Bridge12Technologies/OpenPCBLGR/Model/91780A023.SLDPRT

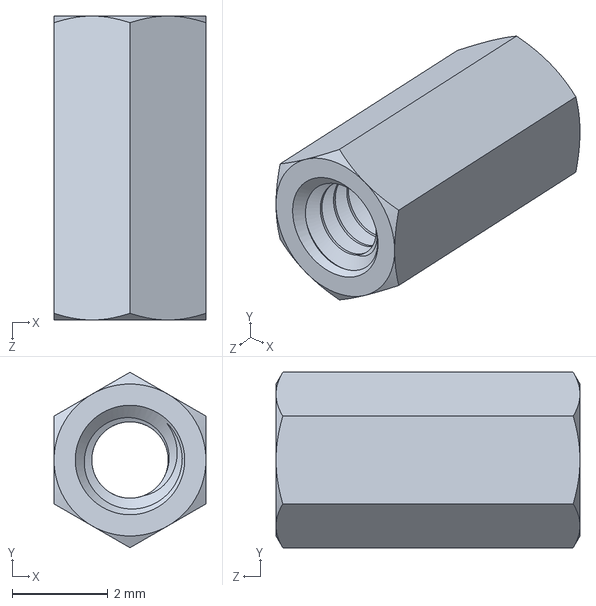
[picture p16: CAD file, 2022-07-21]
Model/91780A023.SLDPRT
3.17 x 3.67 x 6.35 mm
