Bridge12Technologies/OpenPCBLGR/Model/121003110.SLDPRT

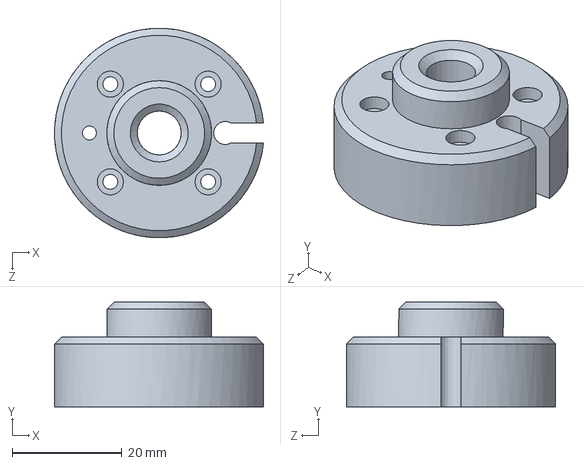
[picture p17: CAD file, 2022-07-21]
Model/121003110.SLDPRT
38.0 x 19.1 x 38.1 mm
