Bridge12Technologies/OpenPCBLGR/KiCAD/5mm_X-Band_LGR/X-Band_EPR_LGR.sch

## KiCad design KiCAD/5mm_X-Band_LGR/X-Band_EPR_LGR.sch (2022-07-21)

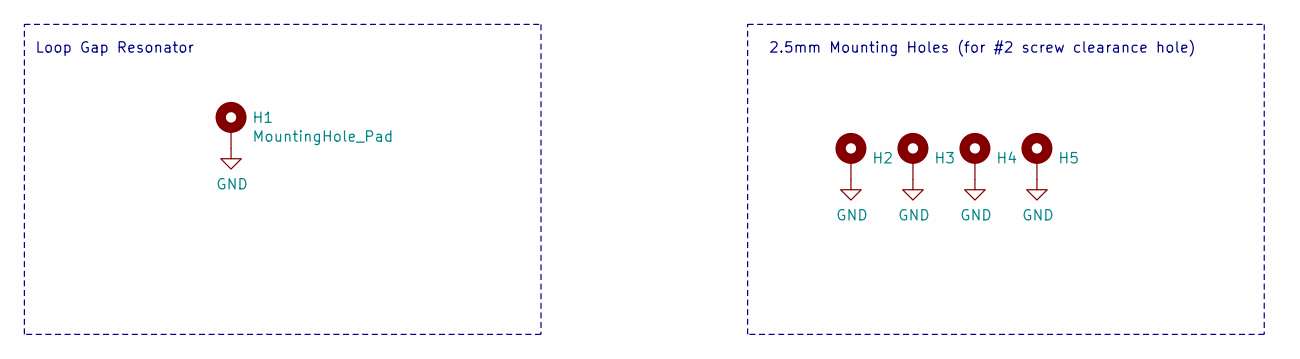
[picture p18: schematic X-Band_EPR_LGR.sch]

Parts:
H1: MountingHole_Pad; 5.2mm_3L2G_X-Band
H2, H3, H4, H5: MountingHole_Pad; MountingHole_2.5mm_Pad

Connections:
GND: H1.1, H2.1, H3.1, H4.1, H5.1

Notes on the sheet:
Loop Gap Resonator
2.5mm Mounting Holes (for #2 screw clearance hole)
