Bridge12Technologies/OpenPCBLGR/KiCAD/5mm_X-Band_LGR_BOTTOM/X-Band_EPR_LGR_BOTTOM.sch

## KiCad design KiCAD/5mm_X-Band_LGR_BOTTOM/X-Band_EPR_LGR_BOTTOM.sch (2022-07-21)

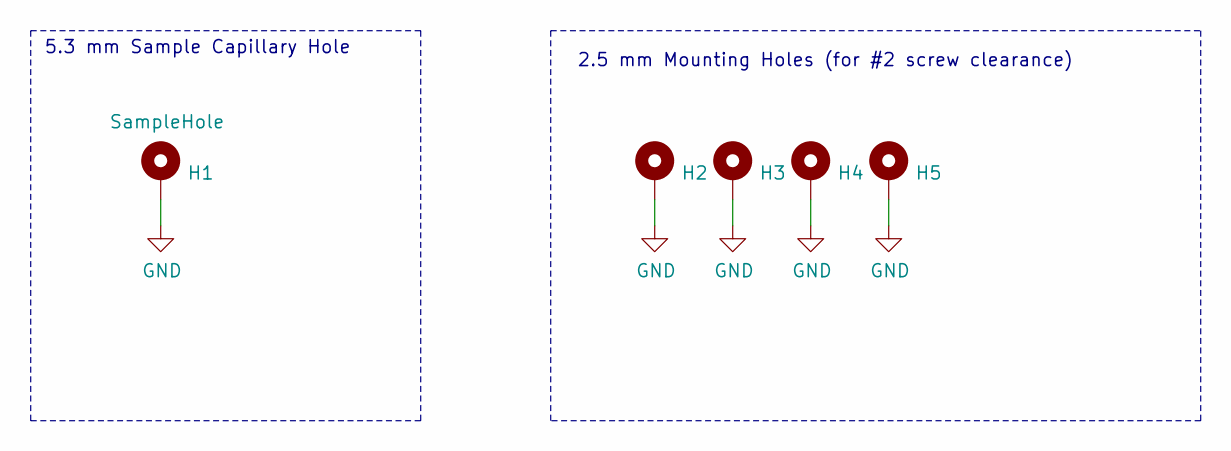
[picture p19: schematic X-Band_EPR_LGR_BOTTOM.sch]

Parts:
H1: SampleHole; MountingHole_5.3mm_M5_DIN965_Pad
H2, H3, H4, H5: MountingHole_Pad; MountingHole_2.5mm_Pad

Connections:
GND: H1.1, H2.1, H3.1, H4.1, H5.1

Notes on the sheet:
2.5 mm Mounting Holes (for #2 screw clearance)
5.3 mm Sample Capillary Hole
