Bridge12Technologies/OpenPCBLGR/KiCAD/5mm_X-Band_LGR_TOP/X-Band_EPR_LGR_TOP.sch

## KiCad design KiCAD/5mm_X-Band_LGR_TOP/X-Band_EPR_LGR_TOP.sch (2022-07-21)

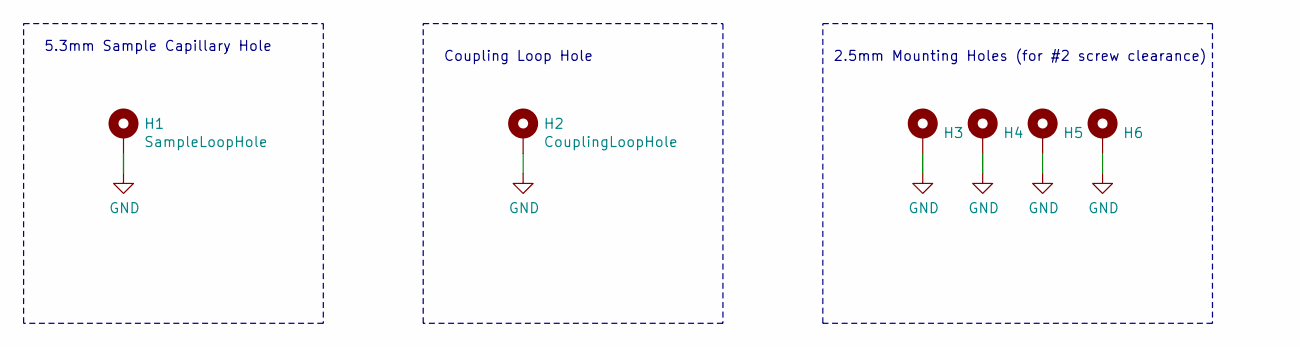
[picture p20: schematic X-Band_EPR_LGR_TOP.sch]

Parts:
H1: SampleLoopHole; MountingHole_5.3mm_M5_DIN965_Pad
H2: CouplingLoopHole; MountingHole_3.7mm_Pad
H3, H4, H5, H6: MountingHole_Pad; MountingHole_2.5mm_Pad

Connections:
GND: H1.1, H2.1, H3.1, H4.1, H5.1, H6.1

Notes on the sheet:
2.5mm Mounting Holes (for #2 screw clearance)
Coupling Loop Hole
5.3mm Sample Capillary Hole
